winedarksea/sirith_pico/usb_pd.kicad_sch

## KiCad design usb_pd.kicad_sch (2025-01-01)

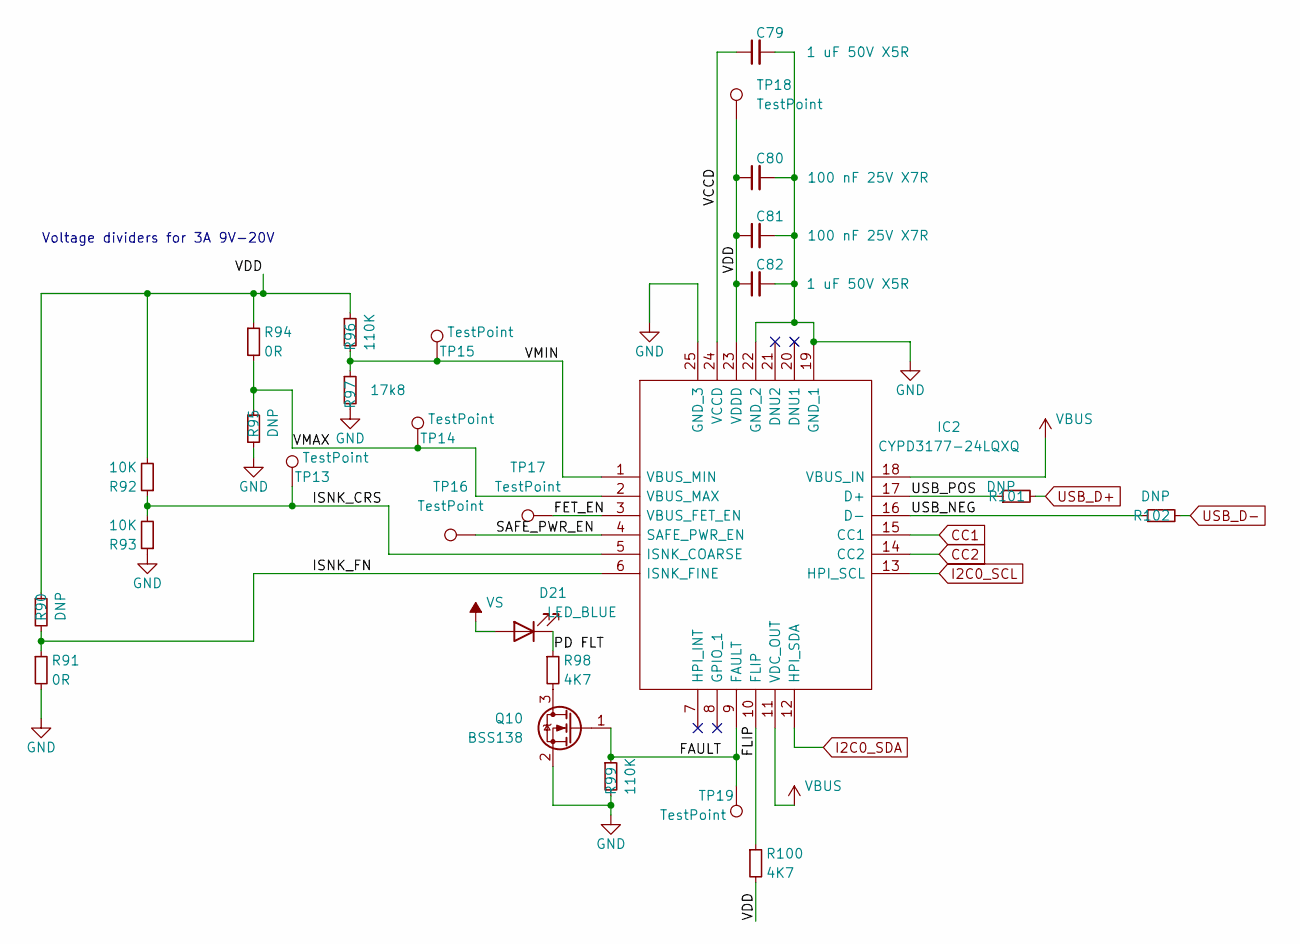
[picture p21: schematic usb_pd.kicad_sch]

Parts:
C79, C82: 1 uF 50V X5R; C_0603_1608Metric
C80, C81: 100 nF 25V X7R; C_0402_1005Metric
D21: LED_BLUE; LED_0603_1608Metric
IC2: CYPD3177-24LQXQ; QFN50P400X400X60-25N-D; Manufacturer_Part_Number CYPD3177-24LQXQ
Q10: BSS138; SOT-23
R90, R95: DNP; R_0603_1608Metric_Pad0.98x0.95mm_HandSolder
R91, R94: 0R; R_1206_3216Metric
R92, R93: 10K; C_0402_1005Metric_Pad0.74x0.62mm_HandSolder
R96, R99: 110K; C_0603_1608Metric
R97: 17k8; C_0402_1005Metric_Pad0.74x0.62mm_HandSolder
R98, R100: 4K7; R_0603_1608Metric_Pad0.98x0.95mm_HandSolder
R101, R102: DNP; R_0402_1005Metric_Pad0.72x0.64mm_HandSolder
TP13, TP14, TP15, TP16, TP17, TP18, TP19: TestPoint; TestPoint_Pad_D1.0mm

Connections:
CC1: IC2.15 (CC1)
CC2: IC2.14 (CC2)
FAULT: IC2.9 (FAULT), Q10.1 (G), R99.1, TP19.1
FET_EN: IC2.3 (VBUS_FET_EN), TP17.1
FLIP: IC2.10 (FLIP), R100.1
GND: C79.2, C80.2, C81.2, C82.2, IC2.19 (GND_1), IC2.22 (GND_2), IC2.25 (GND_3), Q10.2 (S), R91.2, R93.1, R95.2, R97.2, R99.2
I2C0_SCL: IC2.13 (HPI_SCL)
I2C0_SDA: IC2.12 (HPI_SDA)
ISNK_CRS: IC2.5 (ISNK_COARSE), R92.1, R93.2, TP13.1
ISNK_FN: IC2.6 (ISNK_FINE), R90.2, R91.1
unnamed: Q10.3 (D), R98.2
PD FLT: D21.1 (K), R98.1
SAFE_PWR_EN: IC2.4 (SAFE_PWR_EN), TP16.1
USB_D+: R101.2
USB_D-: R102.2
USB_NEG: IC2.16 (D-), R102.1
USB_POS: IC2.17 (D+), R101.1
VBUS: IC2.11 (VDC_OUT), IC2.18 (VBUS_IN)
VCCD: C79.1, IC2.24 (VCCD)
VDD: C80.1, C81.1, C82.1, IC2.23 (VDDD), R90.1, R92.2, R94.1, R96.1, R100.2, TP18.1
VMAX: IC2.2 (VBUS_MAX), R94.2, R95.1, TP14.1
VMIN: IC2.1 (VBUS_MIN), R96.2, R97.1, TP15.1
VS: D21.2 (A)

Notes on the sheet:
Voltage dividers for 3A 9V-20V
